alberand/blueled/docs/XKB-Enterprise-DC-005-5A-2-0_C381116.pdf

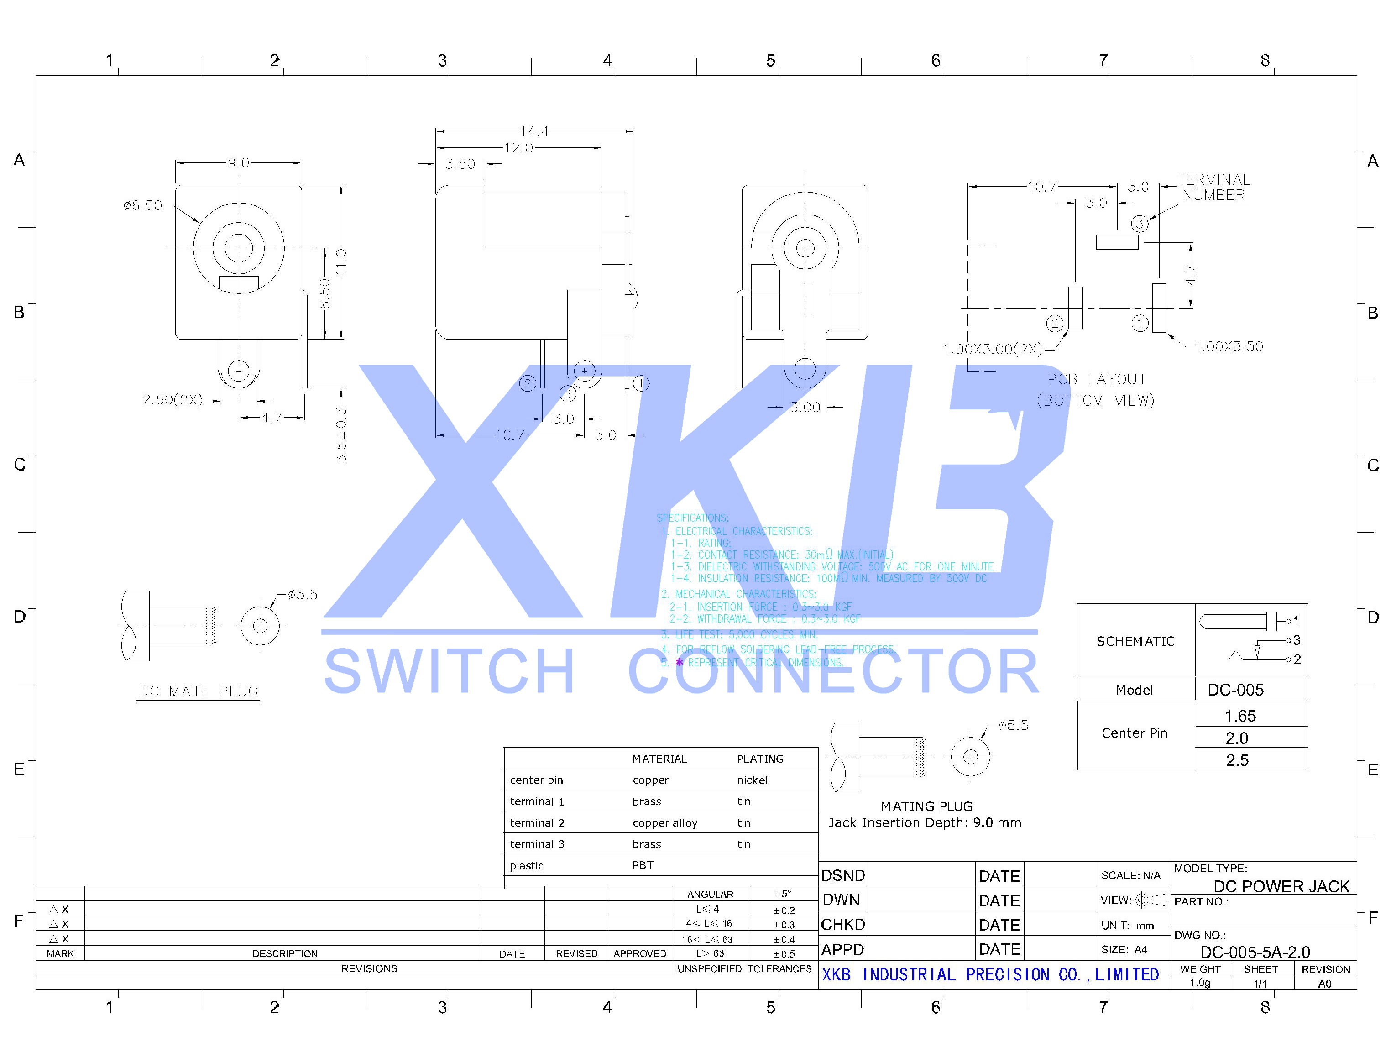
[picture p2: page 1]
