alberand/blueled/docs/XKB-Enterprise-XKB7070-Z_C318863.pdf

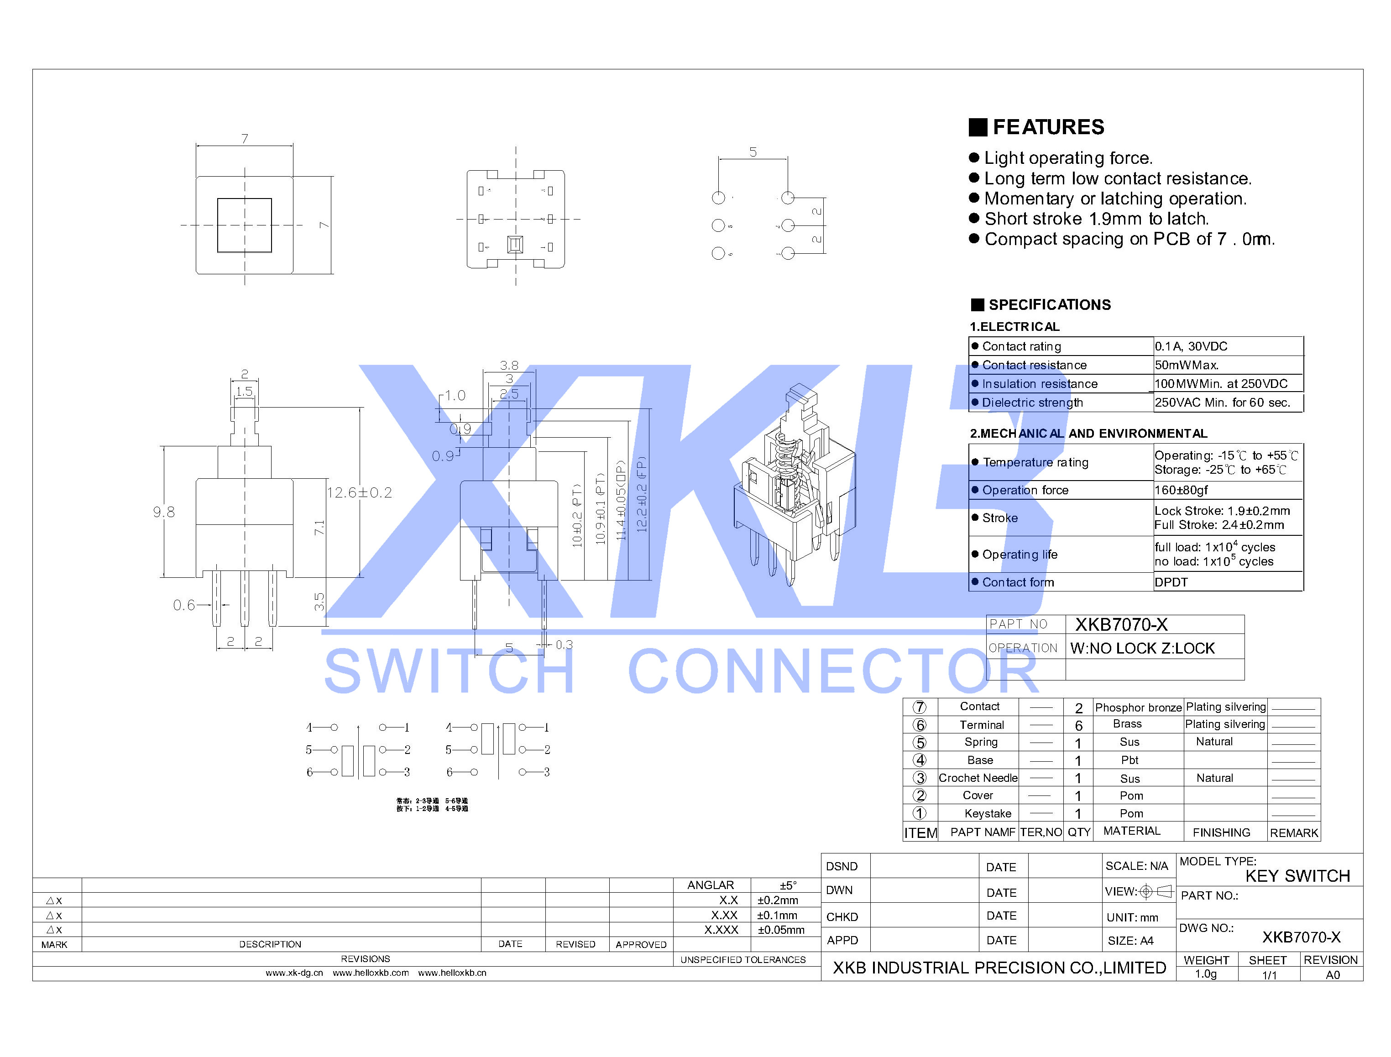
[picture p3: page 1]
